zou-shui/MugglesWand/3.Software/3.POVTool/光绘素材/Star.png

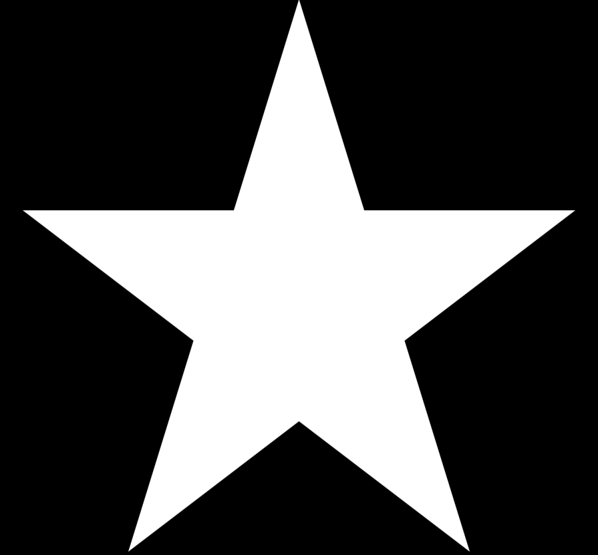
3.Software/3.POVTool/光绘素材/Star.png
